AdrianTunkin/crystal_vision_hud/documents/PATENT/2.png

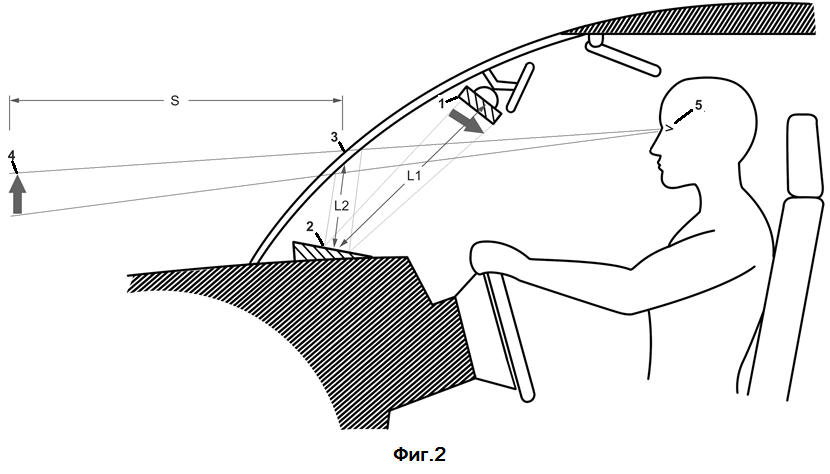
documents/PATENT/2.png
